bocabob/LCC-RPi-Pico-Board/Documentation/LCCPicoNodev2.7 back layout.pdf

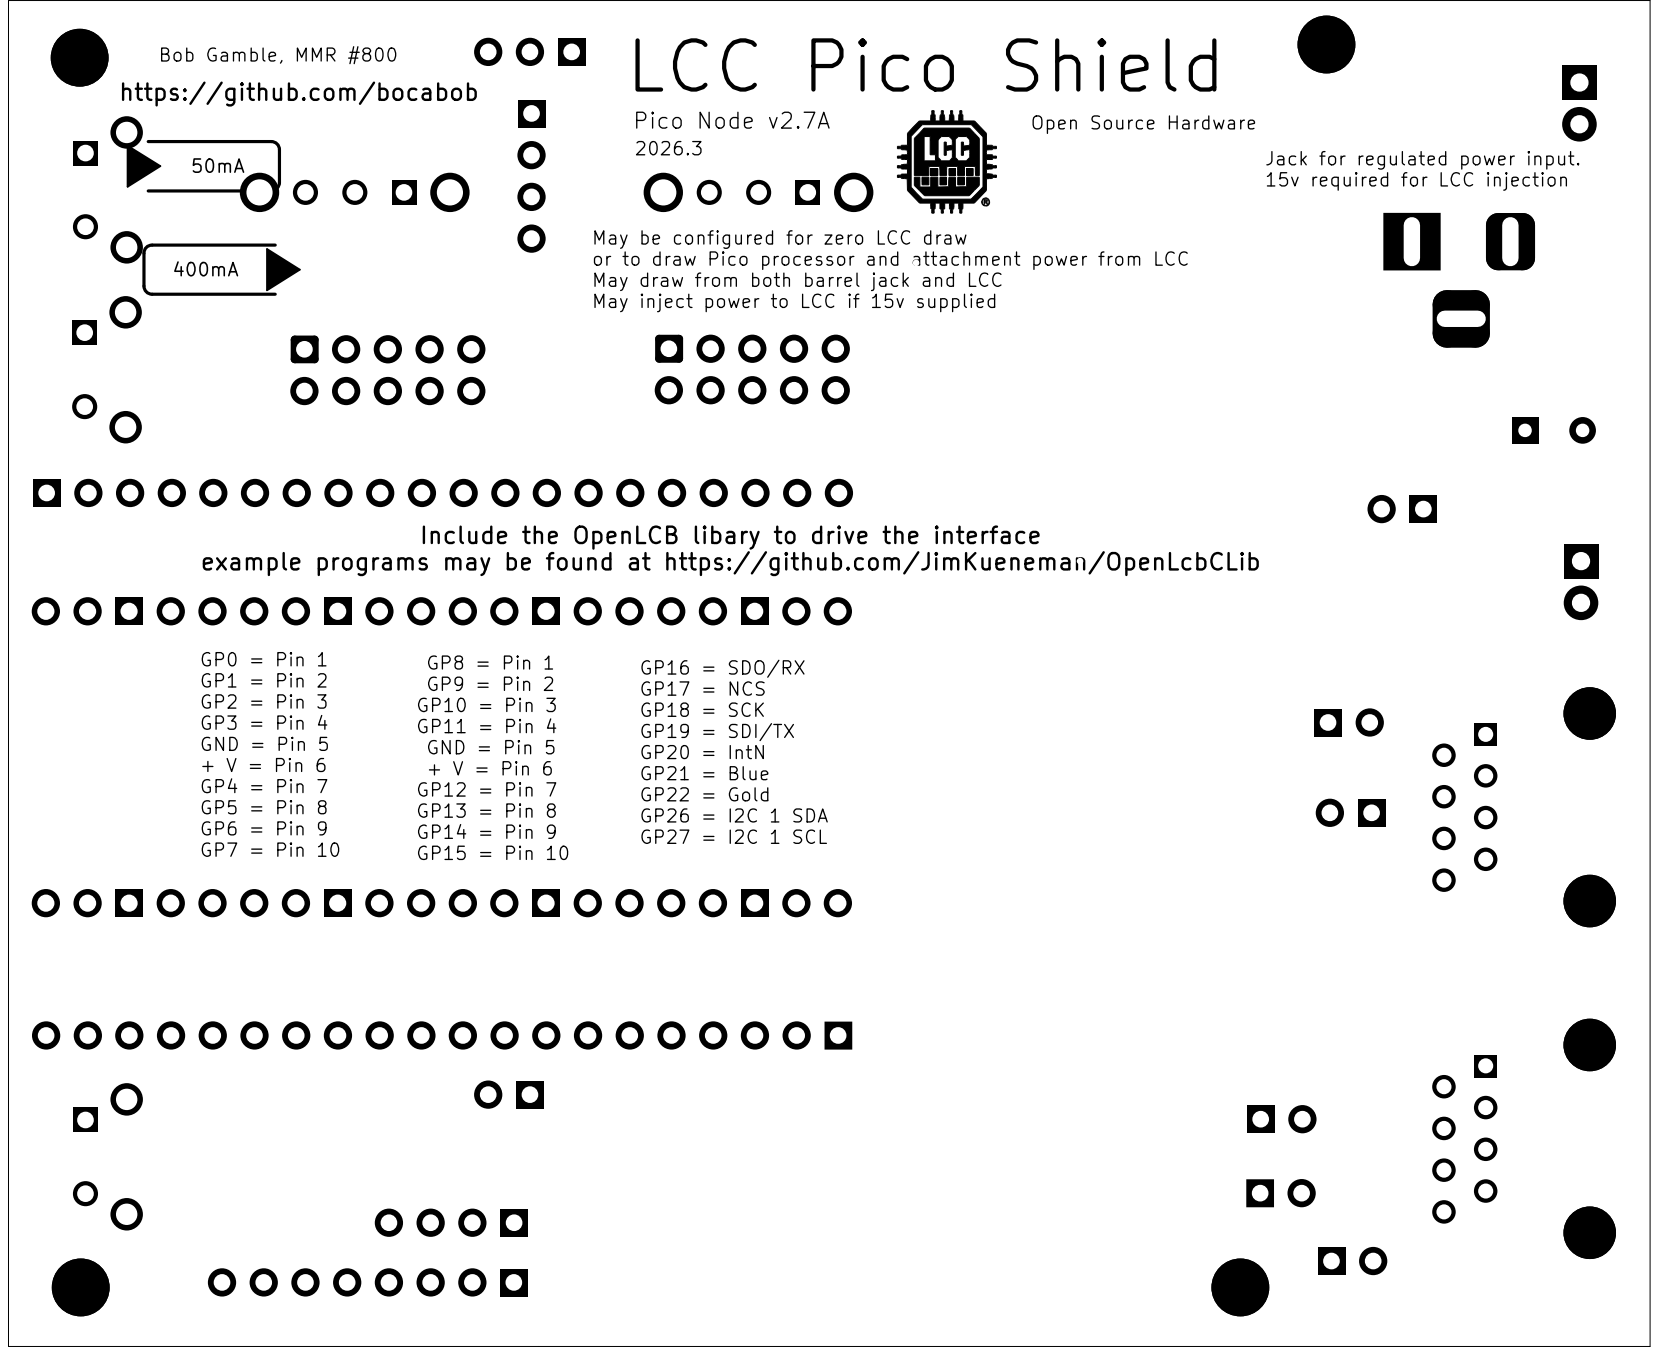
[picture p114: page 1]
