bocabob/LCC-RPi-Pico-Board/Documentation/24A.pdf

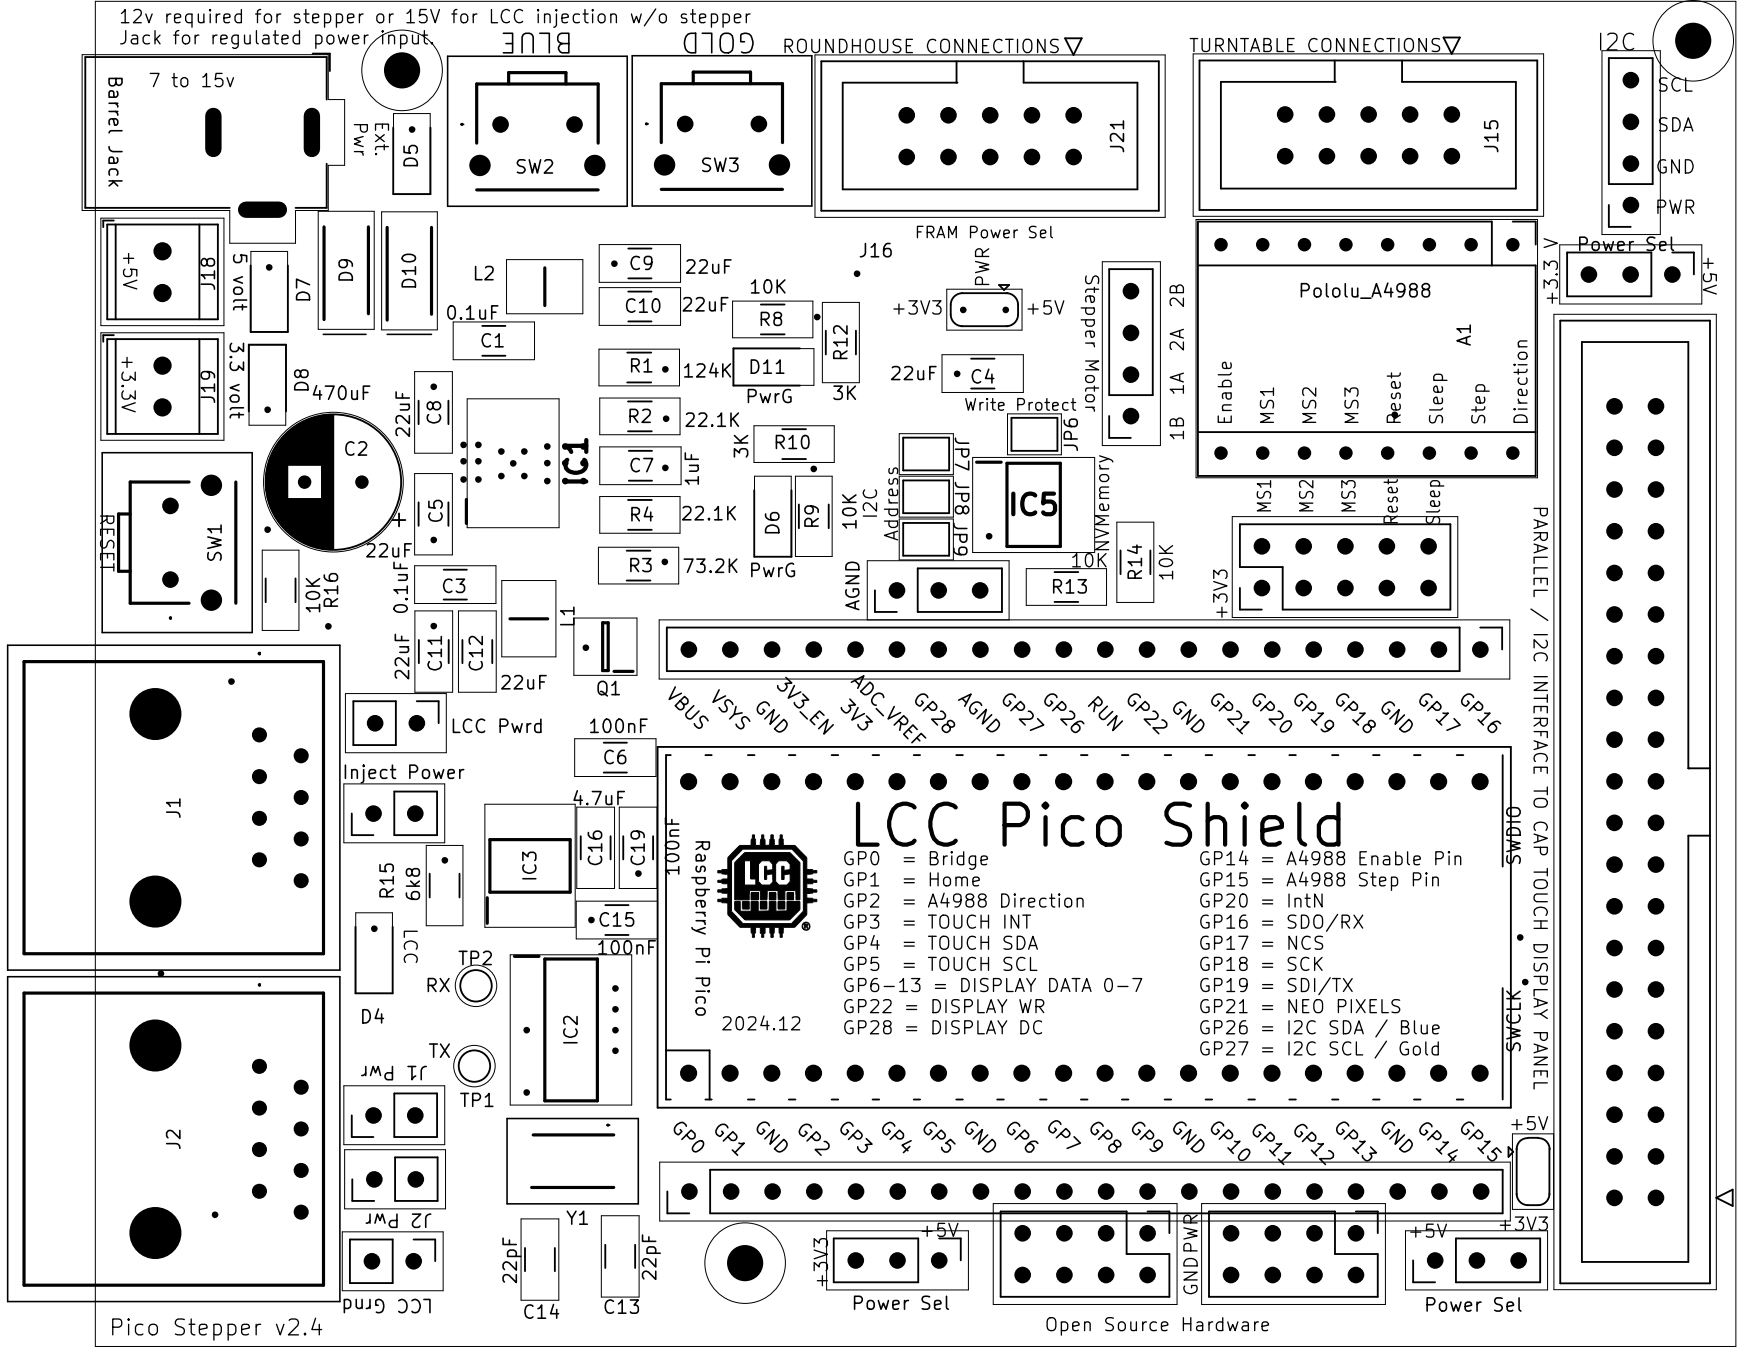
[picture p115: page 1]
