bocabob/LCC-RPi-Pico-Board/Documentation/24B.pdf

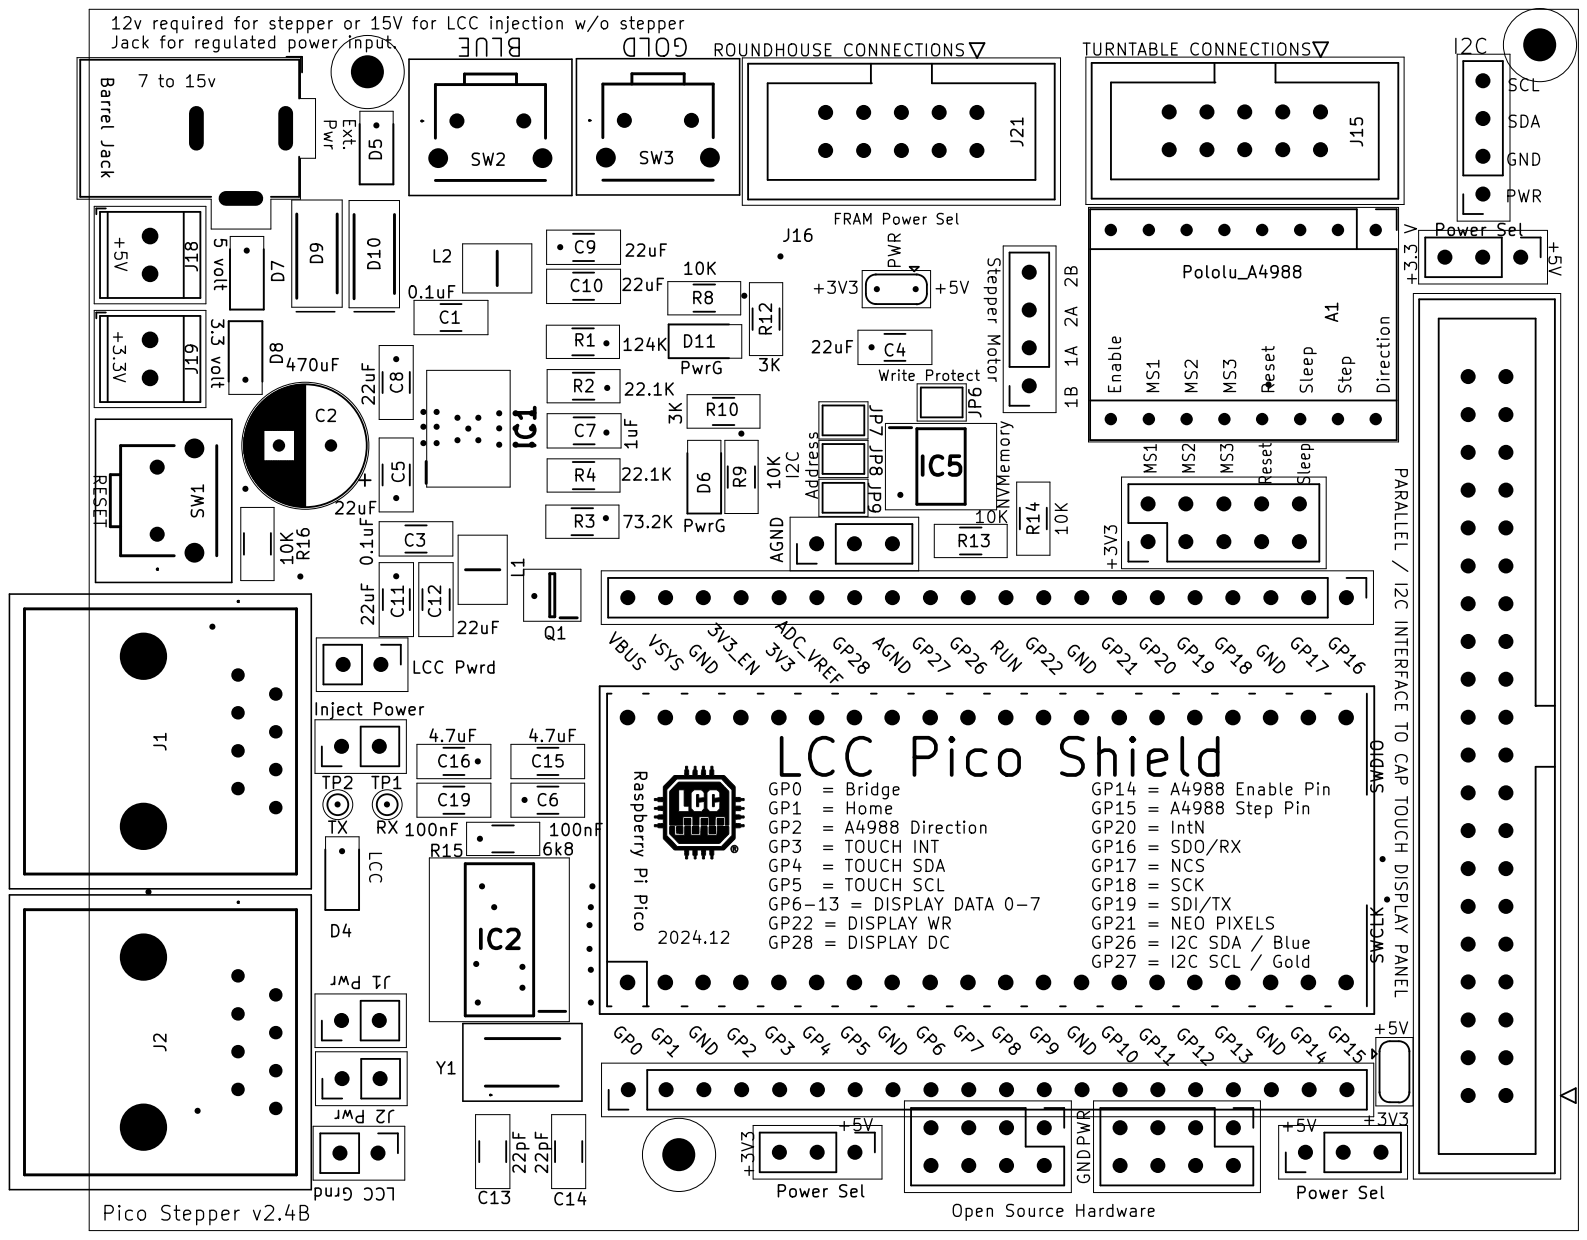
[picture p116: page 1]
