bocabob/LCC-RPi-Pico-Board/Documentation/LCCPicoNodev2.4 layout.pdf

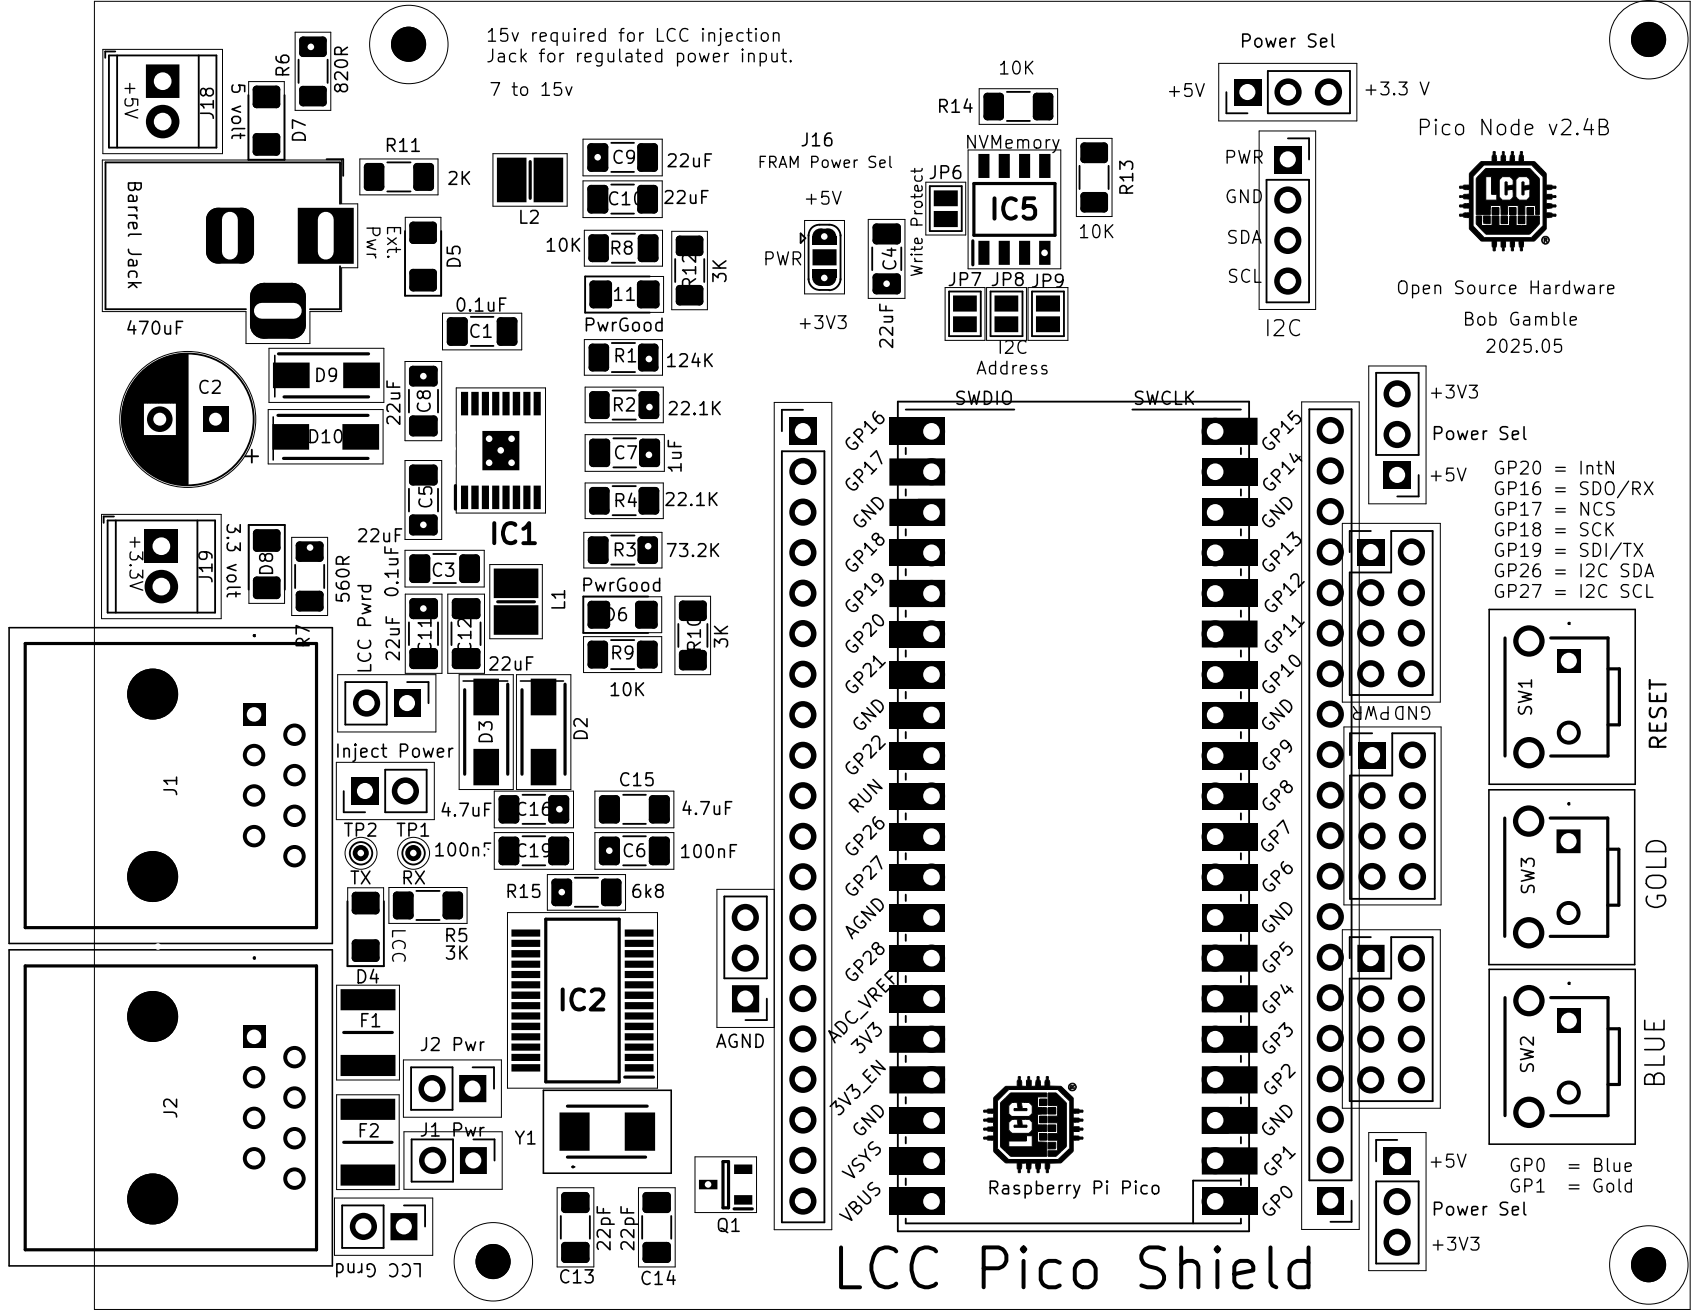
[picture p117: page 1]
