bocabob/LCC-RPi-Pico-Board/Documentation/LCCPicoNodev2.5 layout.pdf

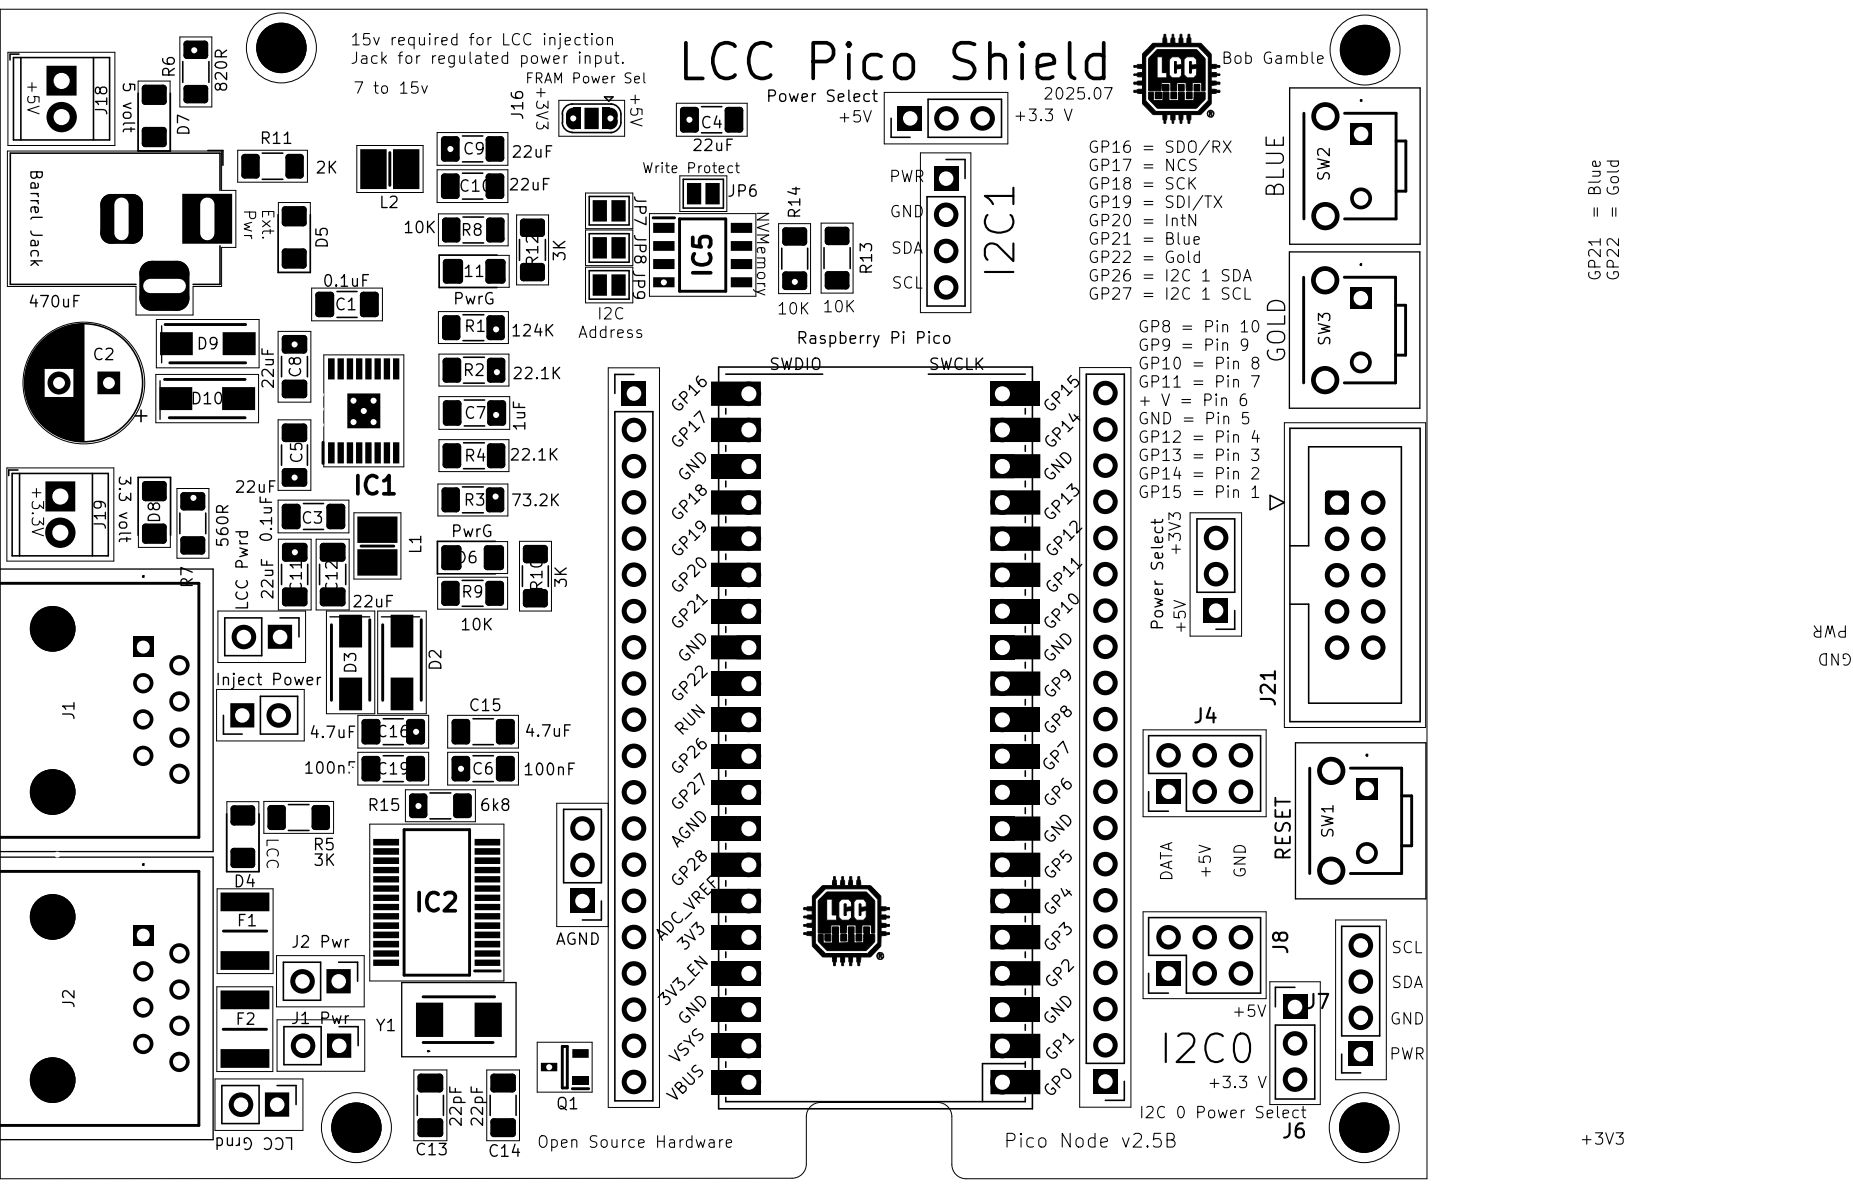
[picture p118: page 1]
