bocabob/LCC-RPi-Pico-Board/Documentation/LCCPicoNode V2.7 Schematic.pdf

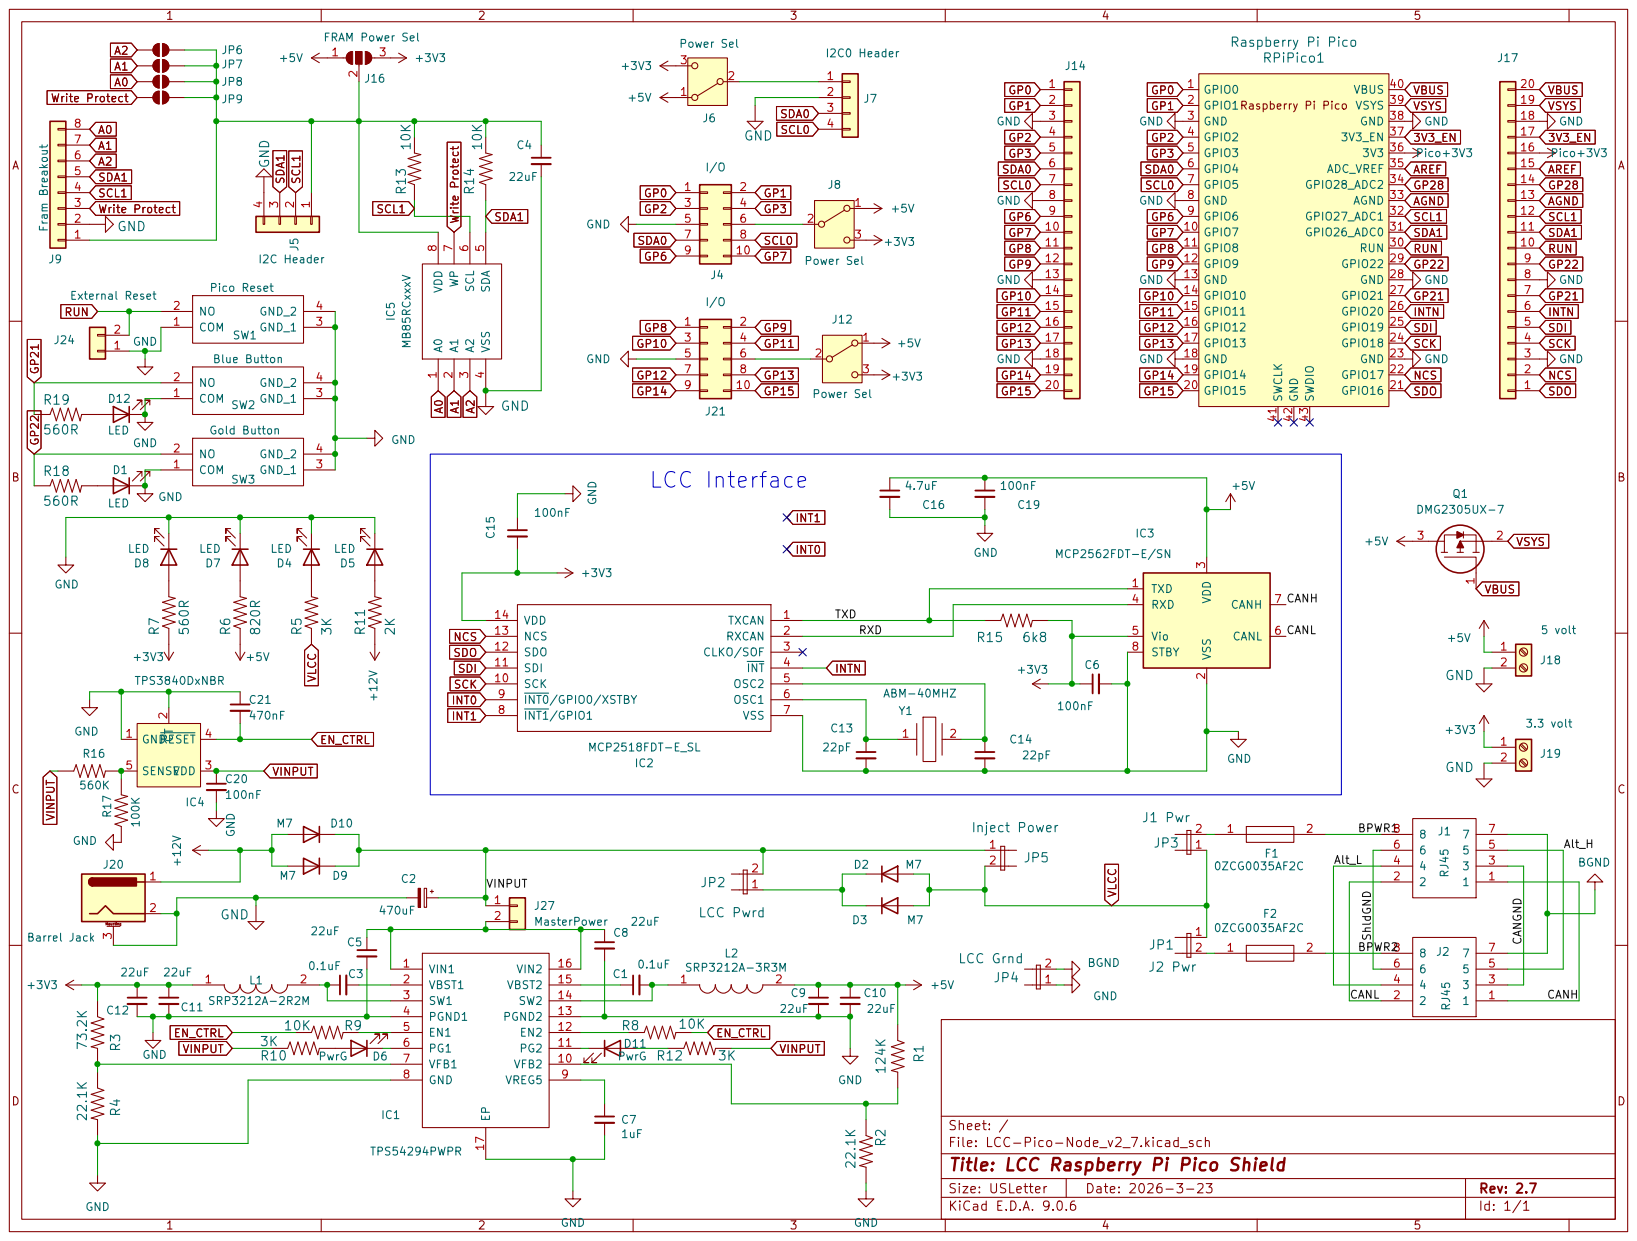
[picture p119: page 1]
