bocabob/LCC-RPi-Pico-Board/RibbonBreakout2.kicad_pcb

## KiCad design RibbonBreakout2.kicad_pcb (2026-07-04)

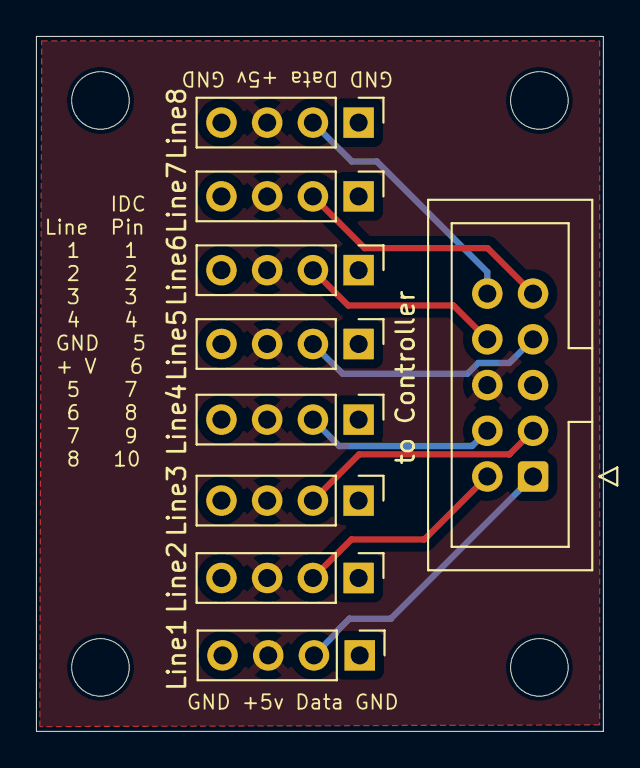
[picture p132: board RibbonBreakout2.kicad_pcb from above]

Board: 2 copper layers, 31.5 x 38.6 mm, 9 parts (0 on the bottom side), 10 nets.

Parts:
Line1, Line2, Line3, Line4, Line5, Line6, Line7, Line8: Header; PinHeader_1x04_P2.54mm_Vertical
S1: Conn_02x05_Odd_Even; IDC-Header_2x05_P2.54mm_Vertical

Connections:
+5v: Line1.3, Line2.3, Line3.3, Line4.3, Line5.3, Line6.3, Line7.3, Line8.3, S1.6
GND: Line1.1, Line1.4, Line2.1, Line2.4, Line3.1, Line3.4, Line4.1, Line4.4, Line5.1, Line5.4, Line6.1, Line6.4, Line7.1, Line7.4, Line8.1, Line8.4, S1.5
Line1: Line1.2, S1.1
Line2: Line2.2, S1.2
Line3: Line3.2, S1.3
Line4: Line4.2, S1.4
Line5: Line5.2, S1.7
Line6: Line6.2, S1.8
Line7: Line7.2, S1.9
Line8: Line8.2, S1.10
