bocabob/LCC-RPi-Pico-Board/RibbonBreakout.kicad_pcb

## KiCad design RibbonBreakout.kicad_pcb (2026-01-22, an earlier design)

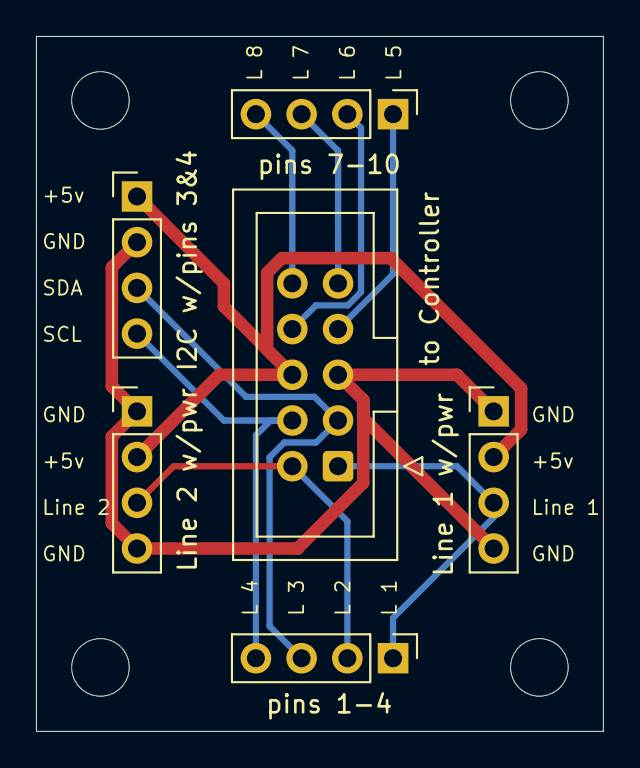
[picture p133: board RibbonBreakout.kicad_pcb from above]

Board: 2 copper layers, 31.5 x 38.6 mm, 6 parts (0 on the bottom side), 10 nets.

Parts:
J1, J2, J3, J4, J5: PinHeader_1x04_P2.54mm_Vertical
S1: Conn_02x05_Odd_Even; IDC-Header_2x05_P2.54mm_Vertical

Connections:
+5v: J1.2, J2.2, J5.1, S1.6
GND: J1.1, J1.4, J2.1, J2.4, J5.2, S1.5
Line1: J1.3, J3.1, S1.1
Line2: J2.3, J3.2, S1.2
Line3: J3.3, J5.3, S1.3
Line4: J3.4, J5.4, S1.4
Line5: J4.1, S1.7
Line6: J4.2, S1.8
Line7: J4.3, S1.9
Line8: J4.4, S1.10
